kervel/waterput_esp8266/pics/IMG_20200826_212548.jpg

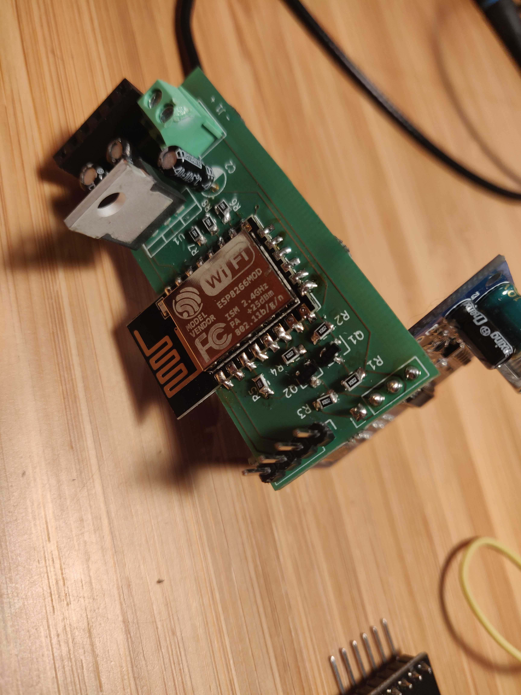
pics/IMG_20200826_212548.jpg
